emc2cube/MySRaspiGW/Regular/V1/img/MySRaspiGW.jpg

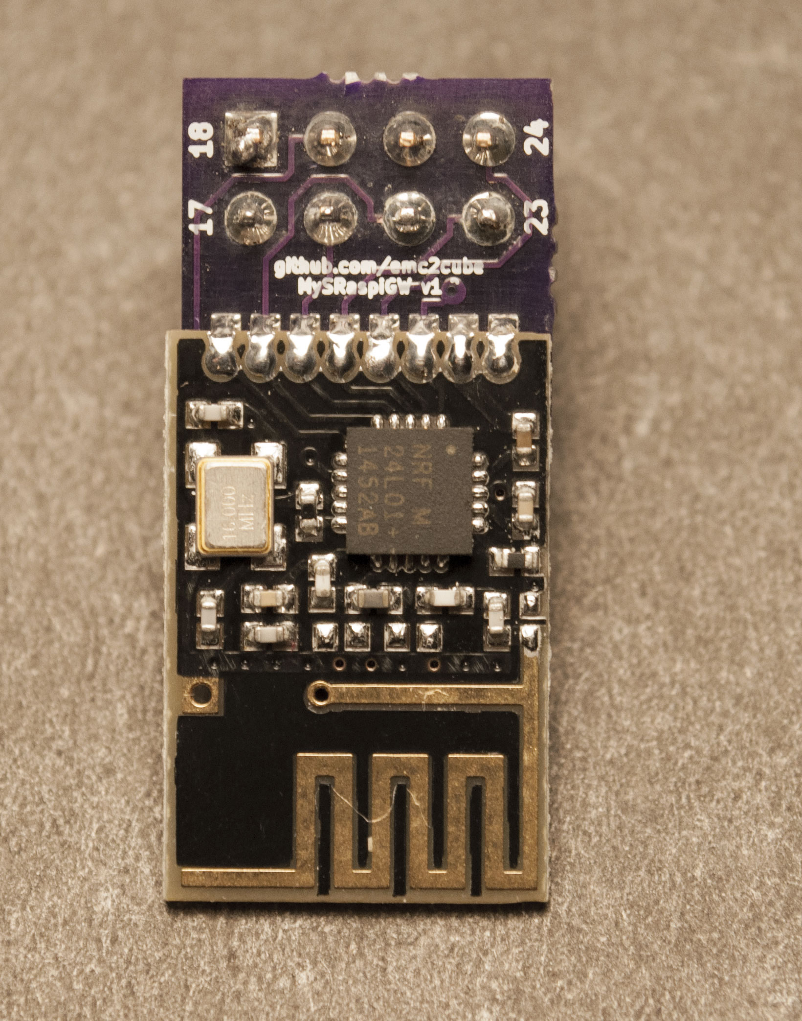
Regular/V1/img/MySRaspiGW.jpg
